johnnyvenom/noisebox/Noisebox-2015-resources/Noisebox-2015-boxes/lasercutter-files/noisebox-box6_3in-sides.dxf

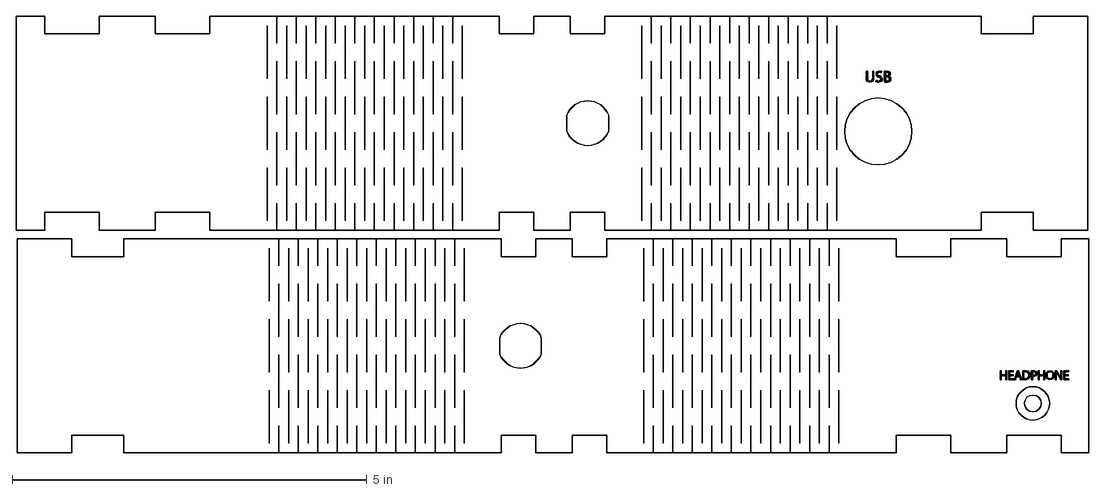
[picture p17: CAD file, 2017-06-23]
Noisebox-2015-resources/Noisebox-2015-boxes/lasercutter-files/noisebox-box6_3in-sides.dxf
15.1 x 6.15 in
